SimpleMethod/7SegmentDisplayClock/SourceCode/Core/Inc/gps_neo6.h

#ifndef gps_neo6_h
#define gps_neo6_h

#define GPS_UART_BUFFER_SIZE 256
#define GPS_WORKING_BUFFER_SIZE 128
typedef struct
{

	UART_HandleTypeDef *neo6_huart;
	uint8_t UartBuffer[GPS_UART_BUFFER_SIZE];
	uint8_t UartBufferHead;
	uint8_t UartBufferTail;
	uint8_t UartBufferLines;

	uint8_t WorkingBuffer[GPS_WORKING_BUFFER_SIZE];

	uint8_t Hour;
	uint8_t Minute;
	uint8_t Second;
	uint8_t Day;
	uint8_t Month;
	uint8_t Year;


}NEO6_State;

NEO6_State GpsState;

void NEO6_Init(NEO6_State *GpsStateHandler, UART_HandleTypeDef *huart);
void NEO6_ReceiveUartChar(NEO6_State *GpsStateHandler);
void NEO6_Task(NEO6_State *GpsStateHandler);

uint8_t NEO6_IsFix(NEO6_State *GpsStateHandler);

#endif /* gps_neo6_h */
